martin075/8xDS18x20_bmp085_LCD_UART/owi_highlevel.h

#ifndef _OWI_HIGHLEVEL_
#define _OWI_HIGHLEVEL_

#include <avr/io.h>

#include "owi_defs.h"
#include "owi_lowlevel.h"

#define OWI_FAMILY( c) (c & 0x7F)	// oem/custom devices have high bit set

#define	OWI_SEARCH_FIRST 0xFF	// start new search
#define OWI_LAST_DEVICE 0x00	// last device found
// 0x01 ... 0x40: continue searching

// function declarations
extern uint8_t owi_byte_io( uint8_t b);
extern uint8_t owi_device_command( uint8_t command, uint8_t *id);
extern uint8_t owi_search( uint8_t diff, uint8_t *id, uint8_t cmd);

#endif  // _OWI_HIGHLEVEL_
